72ka/OndraMELODIK/Images/OndraMelodikTisk.jpg

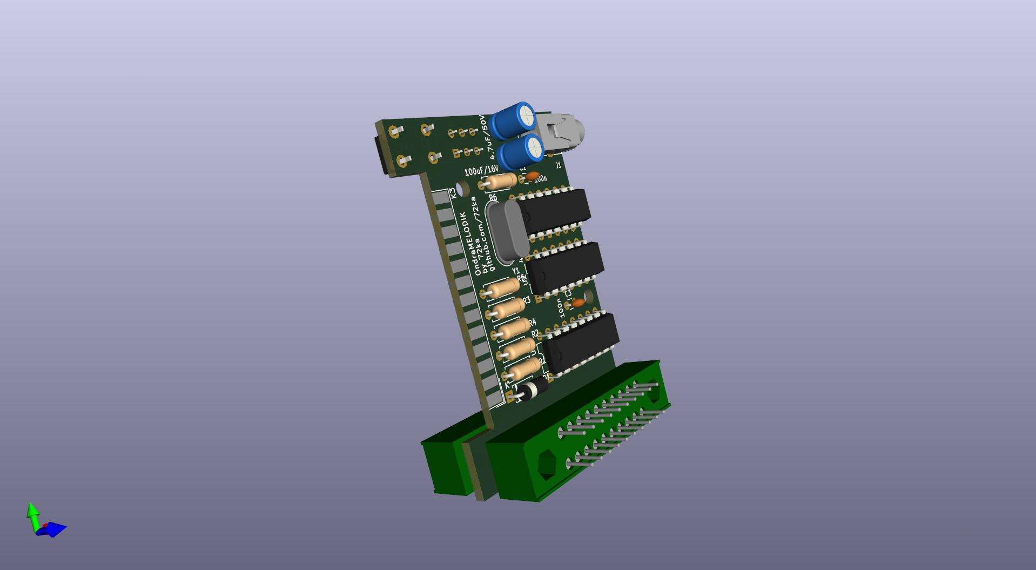
Images/OndraMelodikTisk.jpg
